jmshearer/MiniAppleII/Graphics/OregonTrail/oregon2.png

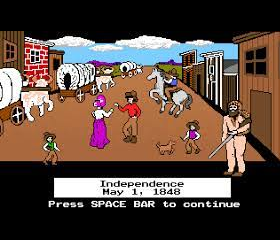
Graphics/OregonTrail/oregon2.png
