jmshearer/MiniAppleII/Graphics/OregonTrail/oregon3.jpg

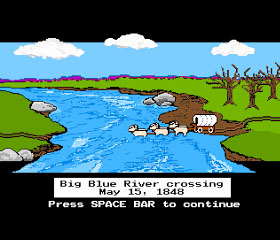
Graphics/OregonTrail/oregon3.jpg
