jmshearer/MiniAppleII/Controller/FullSequence/graphics.h

#ifndef _IMAGE_H_
#define _IMAGE_H_

extern const unsigned char oregon1[];
extern const unsigned char oregon2[];
extern const unsigned char oregon3[];
extern const unsigned char oregon4[];
extern const unsigned char oregon5[];
extern const unsigned char oregon6[];
extern const unsigned char oregon7[];
//extern const unsigned char shearers[];

#endif
